MOSH-Insa-Toulouse/2022-2023-4gp-seguret_selva/LTSpice/Ampli transimpédance.asc

C1: cap; 100n
C2: cap; 100n
C4: cap; 100n
C5: cap; 1p
R1: res; 100k
R2: res; 1k
R3: res; 100k
R4: res; 1k
R5: res; 10k
U1: LTC1050
V1: voltage; 5
V2: voltage; SINE(0 325 50)
V3: voltage; PULSE(0 1 0.2 0.1 0.1 200)
X1: Jauge_Graphite
Named nets: ADC, 0
.tran 12
