MOSH-Insa-Toulouse/2022-2023-4gp-seguret_selva/LTSpice/Jauge_Graphite.asc

B1: bi; I=V(cp,cn)*(10n+V(gc,gn)*10n)
C1: cap; 200µ
R1: res; 1k
Named nets: cp, cn, gp, gn, gc
